MDLZCOOL/ina229-module-iso/Software/Application/User/BSP/Inc/bsp_uart_fifo.h

/*
 * SPDX-FileCopyrightText: 2026 MDLZCOOL <mdlzcool@foxmail.com>
 *
 * SPDX-License-Identifier: Apache-2.0
 */

#ifndef _BSP_USART_FIFO_H_
#define _BSP_USART_FIFO_H_

#include "cs32l010_hal.h"

#define UART1_FIFO_EN 1
#define UART2_FIFO_EN 0
#define UART3_FIFO_EN 0
#define UART4_FIFO_EN 0
#define UART5_FIFO_EN 0
#define UART6_FIFO_EN 0
#define UART7_FIFO_EN 0
#define UART8_FIFO_EN 0

/* 定义端口号 */
typedef enum {
  COM1 = 1, /* UART1 */
} COM_PORT_E;

/* 定义串口波特率和FIFO缓冲区大小，分为发送缓冲区和接收缓冲区, 支持全双工 */
#if UART1_FIFO_EN == 1
#define UART1_BAUD 115200
#define UART1_TX_BUF_SIZE 256
#define UART1_RX_BUF_SIZE 256
#endif

/* 串口设备结构体 */
typedef struct {
  UART_HandleTypeDef huart; /* 主要用其中的init结构，读回串口参数 */
  uint8_t *pTxBuf;          /* 发送缓冲区 */
  uint8_t *pRxBuf;          /* 接收缓冲区 */
  uint16_t usTxBufSize;     /* 发送缓冲区大小 */
  uint16_t usRxBufSize;     /* 接收缓冲区大小 */
  __IO uint16_t usTxWrite;  /* 发送缓冲区写指针 */
  __IO uint16_t usTxRead;   /* 发送缓冲区读指针 */
  __IO uint16_t usTxCount;  /* 等待发送的数据个数 */

  __IO uint16_t usRxWrite; /* 接收缓冲区写指针 */
  __IO uint16_t usRxRead;  /* 接收缓冲区读指针 */
  __IO uint16_t usRxCount; /* 还未读取的新数据个数 */

  void (*SendBefor)(void);          /* 开始发送之前的回调函数指针 */
  void (*SendOver)(void);           /* 发送完毕的回调函数指针 */
  void (*ReciveNew)(uint8_t _byte); /* 串口收到数据的回调函数指针 */
  void (*IdleLine)(void);           /* 字符间超时中断 */

  __IO uint8_t Sending; /* 正在发送中标志 */
} UART_T;

void bsp_InitUart(void);
void bsp_DeInitUart(void);
void comSendBuf(COM_PORT_E _ucPort, uint8_t *_ucaBuf, uint16_t _usLen);
void comSendChar(COM_PORT_E _ucPort, uint8_t _ucByte);
uint8_t comGetChar(COM_PORT_E _ucPort, uint8_t *_pByte);
void comClearTxFifo(COM_PORT_E _ucPort);
void comClearRxFifo(COM_PORT_E _ucPort);

void bsp_InitUartParam(COM_PORT_E _ucPort, uint32_t BaudRate, uint32_t Parity,
                       uint32_t Mode);
uint8_t comTxEmpty(COM_PORT_E _ucPort);

void comPutRxFifo(COM_PORT_E _ucPort, uint8_t *_buf, uint16_t _len);

void comSetCallbackReciveNew(COM_PORT_E _ucPort, void (*Func)(uint8_t _byte));
void comSetCallbackSendBefor(COM_PORT_E _ucPort, void (*Func)(void));
void comSetCallbackSendOver(COM_PORT_E _ucPort, void (*Func)(void));

uint32_t comGetBaud(COM_PORT_E _ucPort);
void comSetBaud(COM_PORT_E _ucPort, uint32_t _BaudRate);

#endif
